klienn/swine/swine-esp32/swt_certs.h

#pragma once
// Trust anchor for https://<project-ref>.functions.supabase.co
// This is cert #2 from your chain.pem: GTS Root R4 (self-signed).
static const char SUPABASE_ROOT_CA[] PROGMEM = R"(-----BEGIN CERTIFICATE-----
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
7uJW
-----END CERTIFICATE-----)";
